Haimana/MAIANA_BLUE/Firmware/Maiana_Blue_AIS_Firmware_VSCode_PlatformIO/Inc/ConfigFlags.h

/*
 * ConfigFlags.h
 *
 *  Created on: Oct 11, 2021
 *      Author: peter
 */

#ifndef INC_CONFIGFLAGS_H_
#define INC_CONFIGFLAGS_H_

typedef struct
{
  uint32_t magic;
  uint32_t reserved;
  uint32_t flags[5];
} ConfigFlags;

typedef union
{
  ConfigFlags config;
  uint64_t dw[4];
} ConfigPage;

typedef struct
{
  uint32_t magic;
  uint8_t value;
  uint8_t fill[3];
} XOTrim;

typedef struct
{
  uint32_t magic;
  uint8_t pa_level;
  uint8_t fill[3];
} TXConfig;


#endif /* INC_CONFIGFLAGS_H_ */
